DavidBG88/TFG_IC/Diagramas/Arquitectura_Sistema.png

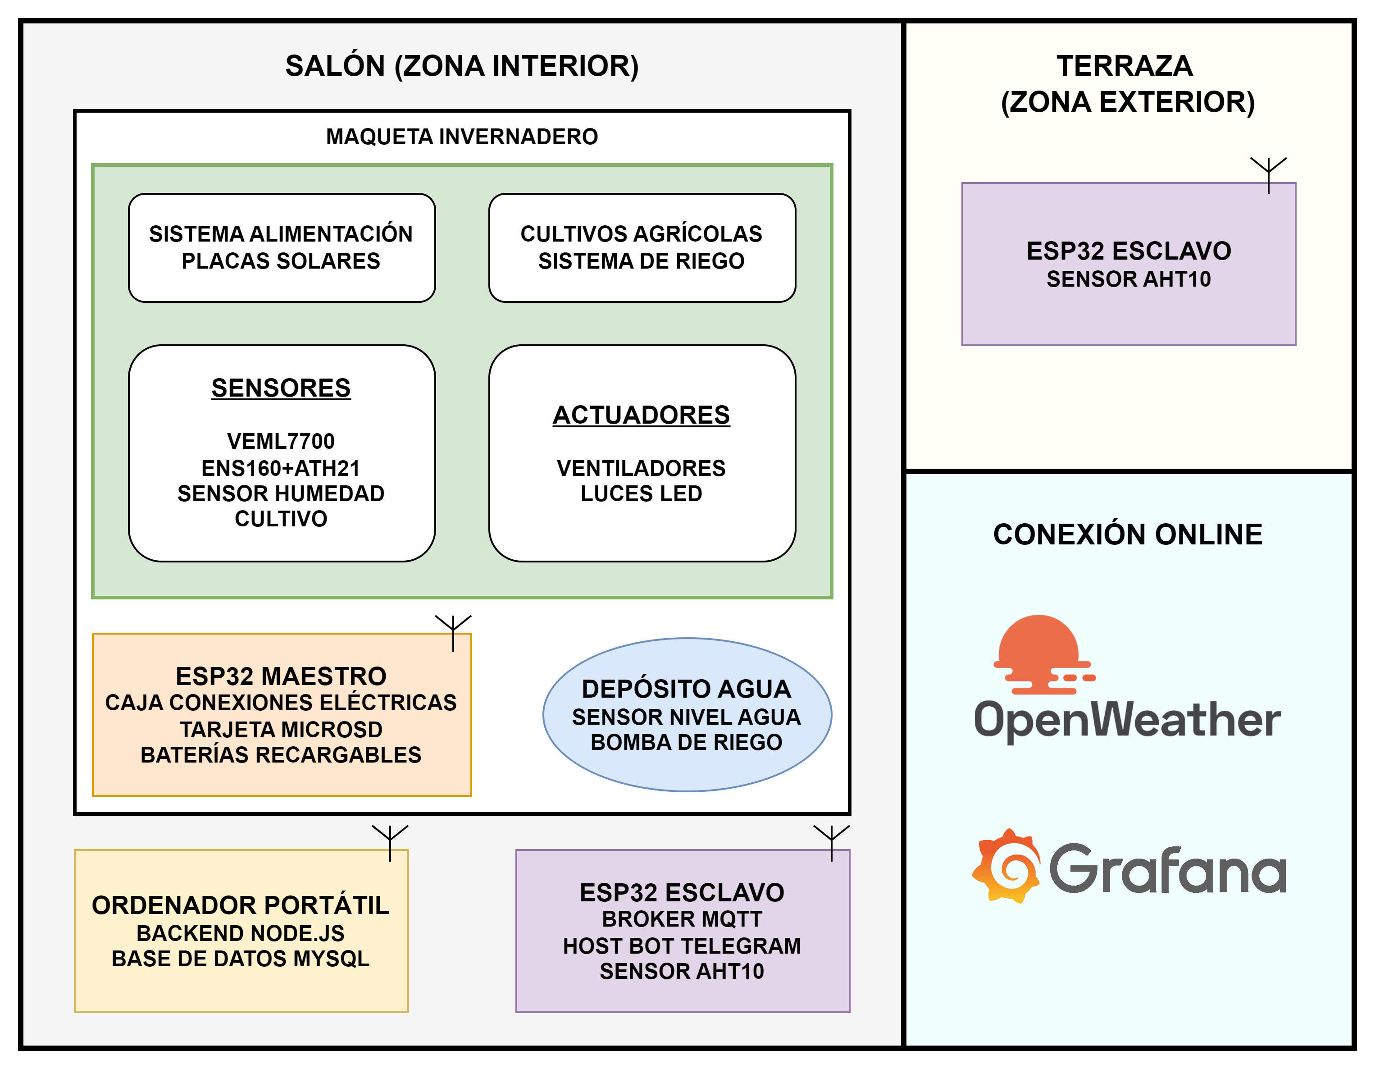
Diagramas/Arquitectura_Sistema.png
