DavidBG88/TFG_IC/Diagramas/Casos_de_Uso.png

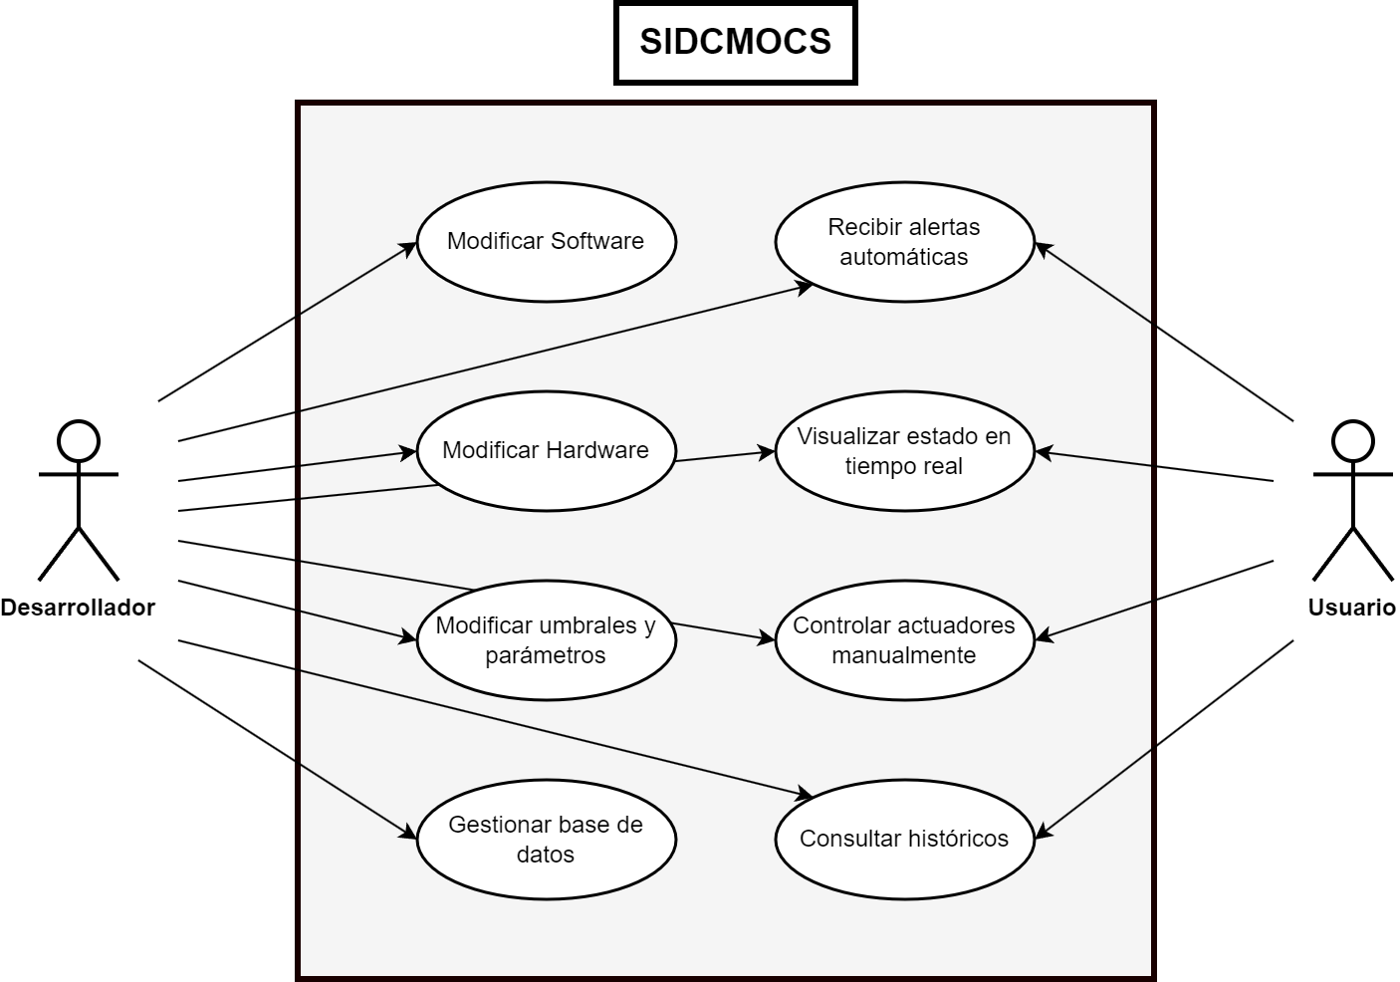
Diagramas/Casos_de_Uso.png
