DavidBG88/TFG_IC/Diagramas/Clases_Esclavo.png

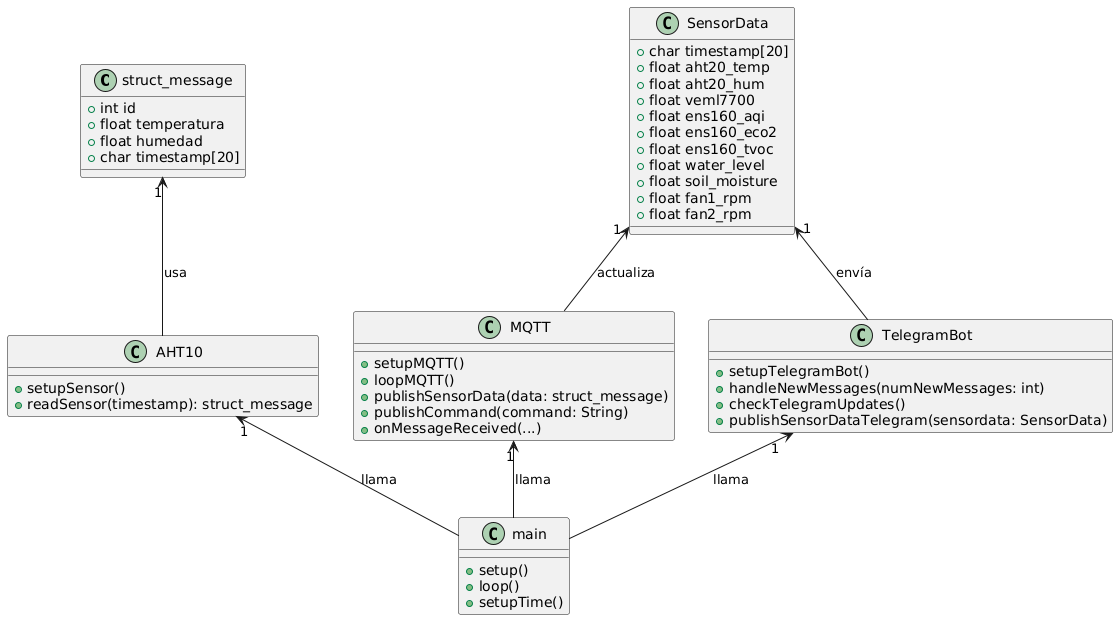
Diagramas/Clases_Esclavo.png
