DavidBG88/TFG_IC/Diagramas/Secuencia/Secuencia_activacionActuadores.png

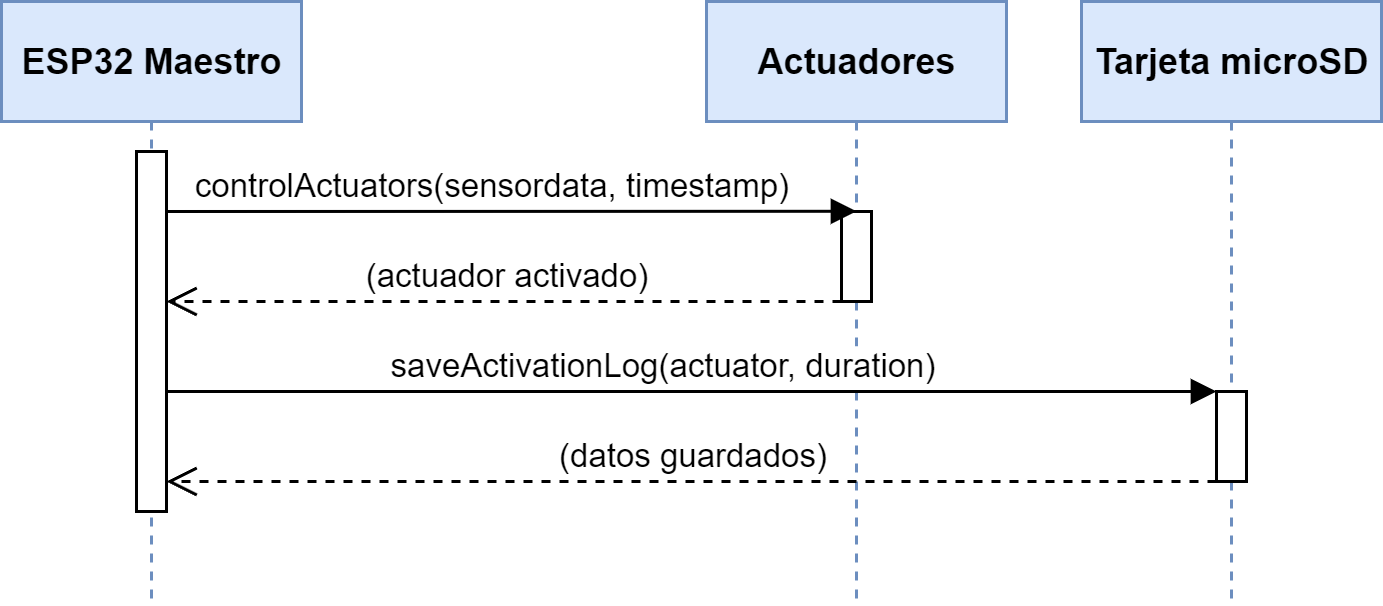
Diagramas/Secuencia/Secuencia_activacionActuadores.png
