DavidBG88/TFG_IC/Diagramas/Secuencia/Secuencia_modopredefinido.png

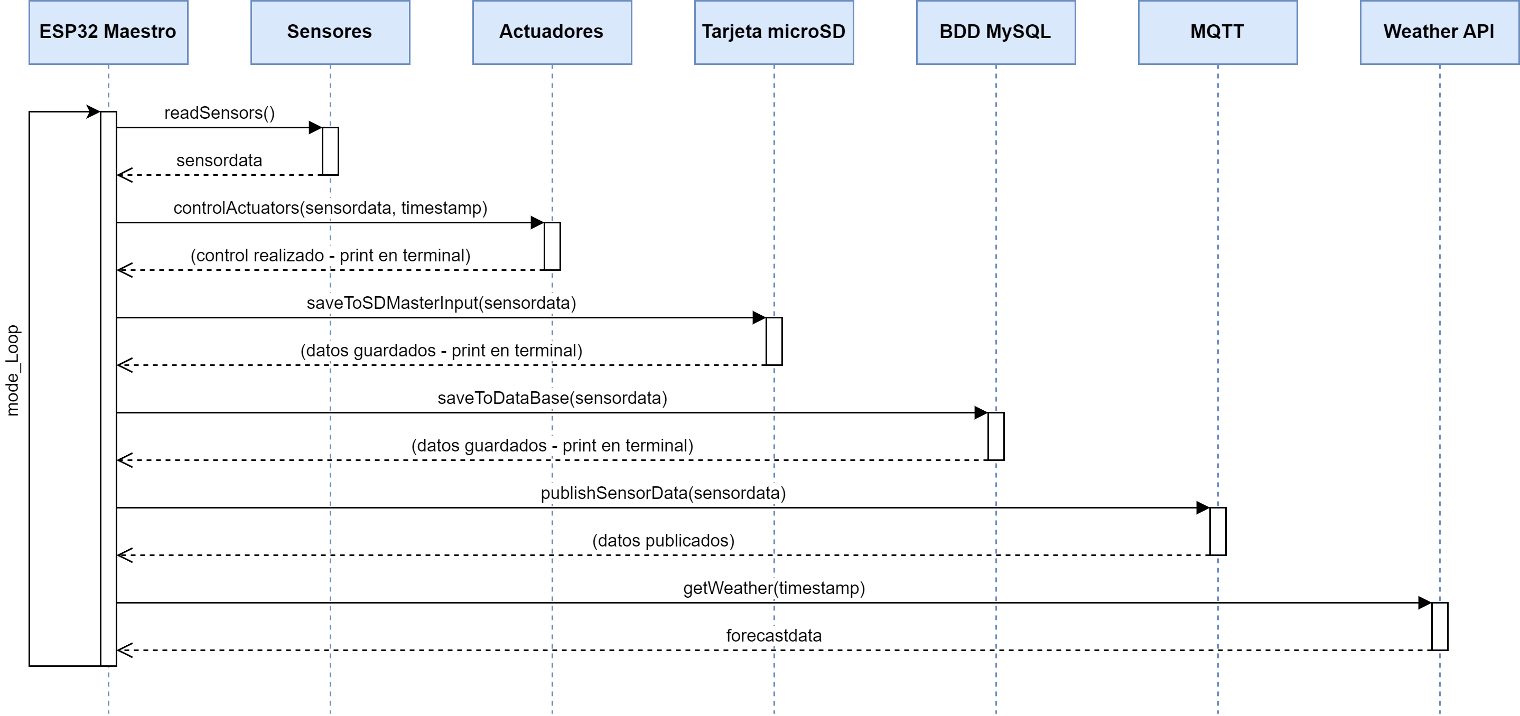
Diagramas/Secuencia/Secuencia_modopredefinido.png
