DavidBG88/TFG_IC/Diagramas/Secuencia/Secuencia_MQTT.png

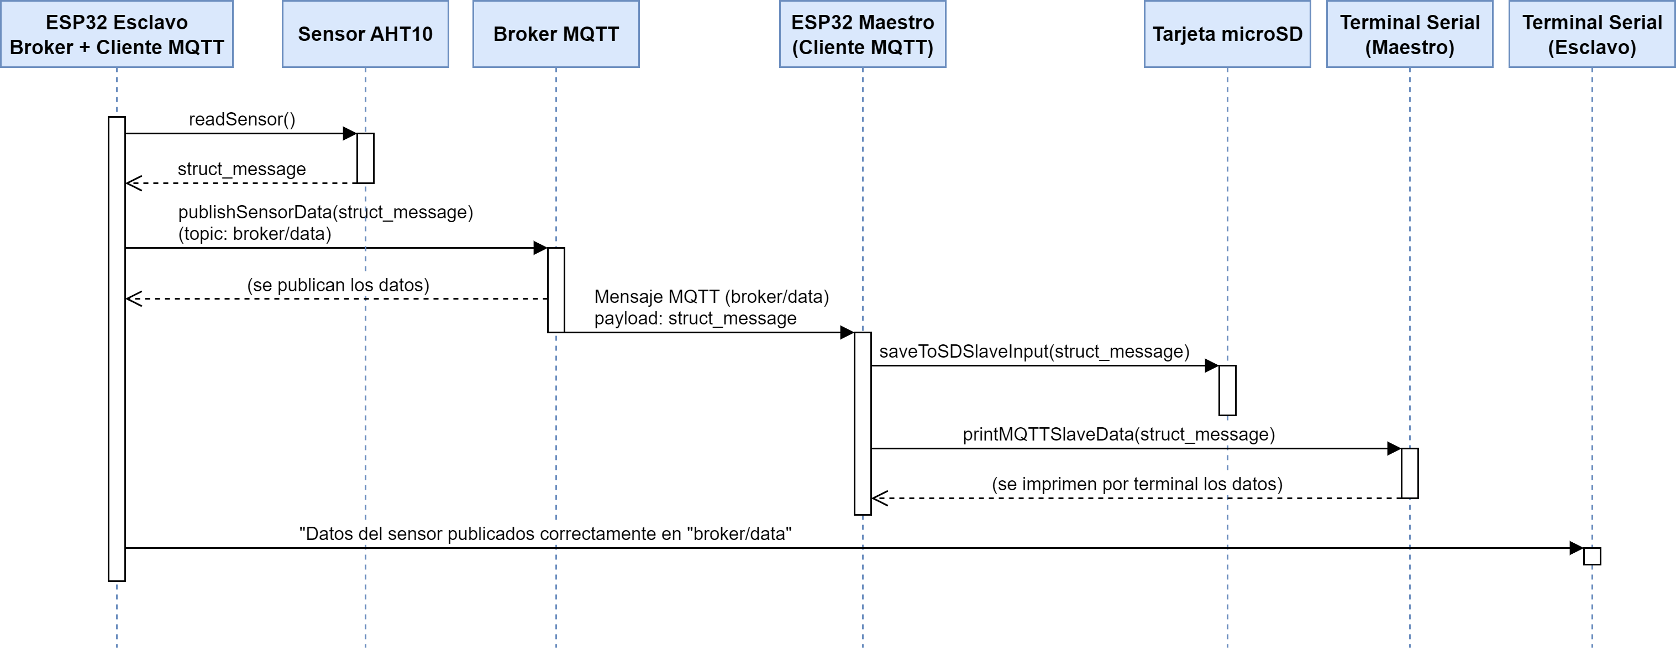
Diagramas/Secuencia/Secuencia_MQTT.png
