DavidBG88/TFG_IC/Diagramas/Componentes.png

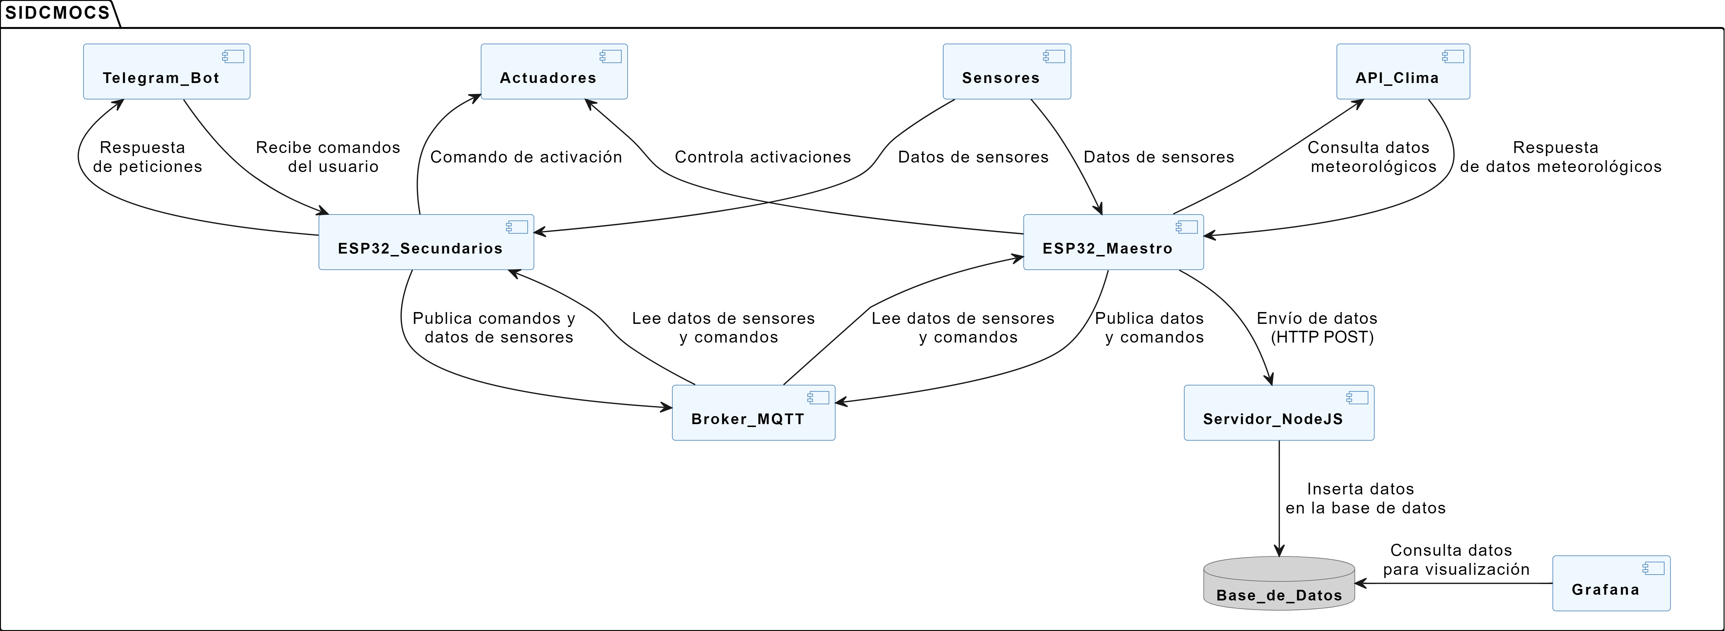
Diagramas/Componentes.png
