DavidBG88/TFG_IC/Diagramas/Secuencia/Secuencia_setup.png

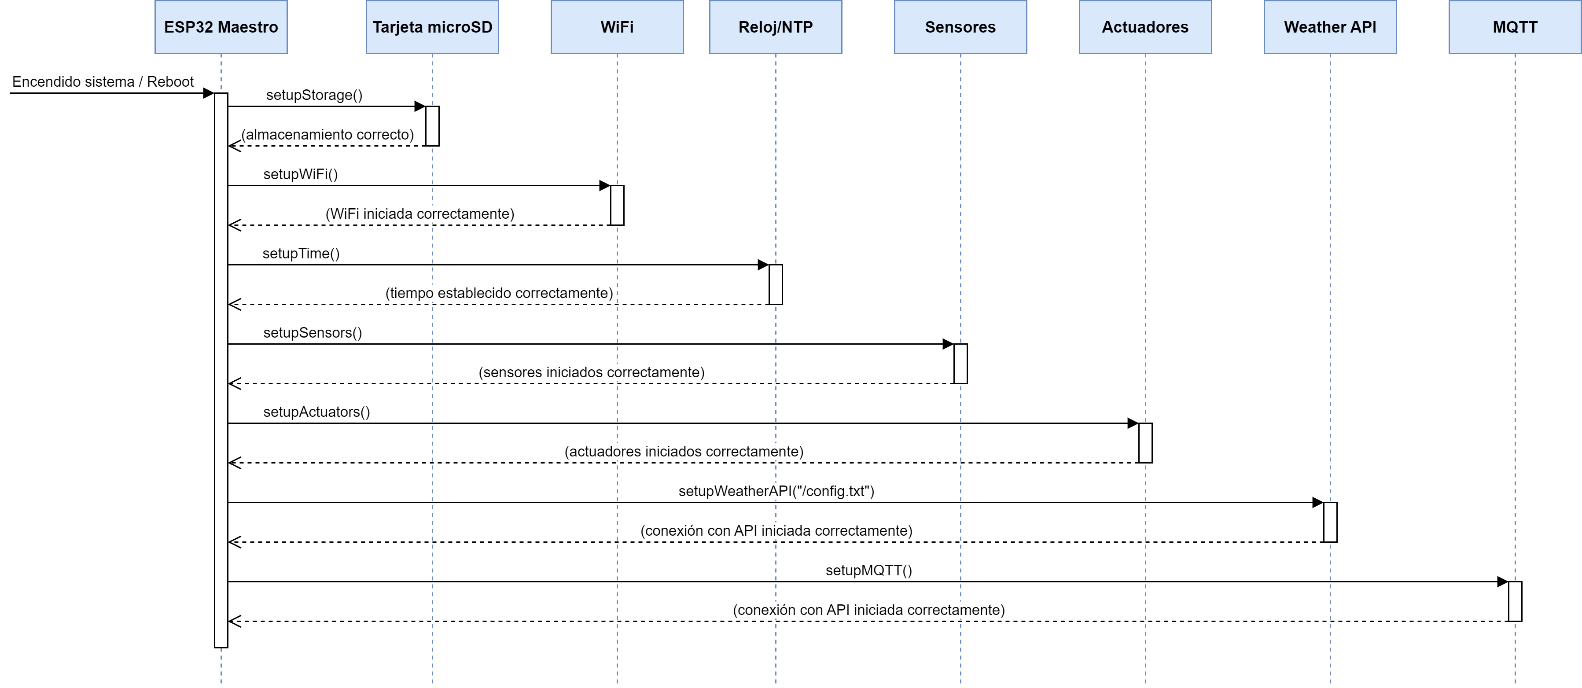
Diagramas/Secuencia/Secuencia_setup.png
